Zaccc11/balance-car-stm32/src/Hardware/mpu6050.c

#include "mpu6050.h"
#include "sys.h"
#include "delay.h"
#include "usart.h"  
#include "MyI2C.h"
#include "MPU6050_Reg.h"
#define MPU6050_ADDRESS		0xD0		//MPU6050的I2C从机地址

//初始化MPU6050
//返回值:0,成功
//其他,错误代码
void MPU6050_Init(void)
{
	MyI2C_Init();									//先初始化底层的I2C
	
	/*MPU6050寄存器初始化，需要对照MPU6050手册的寄存器描述配置，此处仅配置了部分重要的寄存器*/
	MPU_Write_Byte(MPU_PWR_MGMT1_REG,0X80);	//复位MPU6050
	MPU_Write_Byte(MPU_PWR_MGMT1_REG,0X00);
	MPU6050_WriteReg(MPU6050_PWR_MGMT_1, 0x01);		//电源管理寄存器1，取消睡眠模式，选择时钟源为X轴陀螺仪
	MPU6050_WriteReg(MPU6050_PWR_MGMT_2, 0x00);		//电源管理寄存器2，保持默认值0，所有轴均不待机
	MPU6050_WriteReg(MPU6050_SMPLRT_DIV, 0x09);		//采样率分频寄存器，配置采样率
	MPU6050_WriteReg(MPU6050_CONFIG, 0x06);			//配置寄存器，配置DLPF
	MPU6050_WriteReg(MPU6050_GYRO_CONFIG, 0x18);	//陀螺仪配置寄存器，选择满量程为±2000°/s
	MPU6050_WriteReg(MPU6050_ACCEL_CONFIG, 0x18);	//加速度计配置寄存器，选择满量程为±16g
	MPU_Write_Byte(MPU_INTBP_CFG_REG,0X80);	//INT引脚低电平有效
}


uint8_t MPU_GetID(void){
	return MPU_Read_Byte(MPU_DEVICE_ID_REG);
}


void MPU6050_GetData(int16_t *AccX, int16_t *AccY, int16_t *AccZ, 
						int16_t *GyroX, int16_t *GyroY, int16_t *GyroZ)
{
	uint8_t DataH, DataL;								//定义数据高8位和低8位的变量
	
	DataH = MPU6050_ReadReg(MPU6050_ACCEL_XOUT_H);		//读取加速度计X轴的高8位数据
	DataL = MPU6050_ReadReg(MPU6050_ACCEL_XOUT_L);		//读取加速度计X轴的低8位数据
	*AccX = (DataH << 8) | DataL;						//数据拼接，通过输出参数返回
	
	DataH = MPU6050_ReadReg(MPU6050_ACCEL_YOUT_H);		//读取加速度计Y轴的高8位数据
	DataL = MPU6050_ReadReg(MPU6050_ACCEL_YOUT_L);		//读取加速度计Y轴的低8位数据
	*AccY = (DataH << 8) | DataL;						//数据拼接，通过输出参数返回
	
	DataH = MPU6050_ReadReg(MPU6050_ACCEL_ZOUT_H);		//读取加速度计Z轴的高8位数据
	DataL = MPU6050_ReadReg(MPU6050_ACCEL_ZOUT_L);		//读取加速度计Z轴的低8位数据
	*AccZ = (DataH << 8) | DataL;						//数据拼接，通过输出参数返回
	
	DataH = MPU6050_ReadReg(MPU6050_GYRO_XOUT_H);		//读取陀螺仪X轴的高8位数据
	DataL = MPU6050_ReadReg(MPU6050_GYRO_XOUT_L);		//读取陀螺仪X轴的低8位数据
	*GyroX = (DataH << 8) | DataL;						//数据拼接，通过输出参数返回
	
	DataH = MPU6050_ReadReg(MPU6050_GYRO_YOUT_H);		//读取陀螺仪Y轴的高8位数据
	DataL = MPU6050_ReadReg(MPU6050_GYRO_YOUT_L);		//读取陀螺仪Y轴的低8位数据
	*GyroY = (DataH << 8) | DataL;						//数据拼接，通过输出参数返回
	
	DataH = MPU6050_ReadReg(MPU6050_GYRO_ZOUT_H);		//读取陀螺仪Z轴的高8位数据
	DataL = MPU6050_ReadReg(MPU6050_GYRO_ZOUT_L);		//读取陀螺仪Z轴的低8位数据
	*GyroZ = (DataH << 8) | DataL;						//数据拼接，通过输出参数返回
}

uint8_t MPU6050_ReadReg(uint8_t RegAddress)
{
	uint8_t Data;
	
	MyI2C_Start();						//I2C起始
	MyI2C_SendByte(MPU6050_ADDRESS);	//发送从机地址，读写位为0，表示即将写入
	MyI2C_ReceiveAck();					//接收应答
	MyI2C_SendByte(RegAddress);			//发送寄存器地址
	MyI2C_ReceiveAck();					//接收应答
	
	MyI2C_Start();						//I2C重复起始
	MyI2C_SendByte(MPU6050_ADDRESS | 0x01);	//发送从机地址，读写位为1，表示即将读取
	MyI2C_ReceiveAck();					//接收应答
	Data = MyI2C_ReceiveByte();			//接收指定寄存器的数据
	MyI2C_SendAck(1);					//发送应答，给从机非应答，终止从机的数据输出
	MyI2C_Stop();						//I2C终止
	
	return Data;
}

u8 MPU_Get_Gyroscope(short *gx,short *gy,short *gz)
{
    u8 buf[6],res;  
	res=MPU_Read_Len(MPU_ADDR,MPU_GYRO_XOUTH_REG,6,buf);
	if(res==0)
	{
		*gx=((u16)buf[0]<<8)|buf[1];  
		*gy=((u16)buf[2]<<8)|buf[3];  
		*gz=((u16)buf[4]<<8)|buf[5];
	} 	
    return res;;
}

u8 MPU_Get_Accelerometer(short *ax,short *ay,short *az)
{
    u8 buf[6],res;  
	res=MPU_Read_Len(MPU_ADDR,MPU_ACCEL_XOUTH_REG,6,buf);
	if(res==0)
	{
		*ax=((u16)buf[0]<<8)|buf[1];  
		*ay=((u16)buf[2]<<8)|buf[3];  
		*az=((u16)buf[4]<<8)|buf[5];
	} 	
    return res;;
}


//IIC连续写
//addr:器件地址 
//reg:寄存器地址
//len:写入长度
//buf:数据区
//返回值:0,正常
//    其他,错误代码
u8 MPU_Write_Len(u8 addr,u8 reg,u8 len,u8 *buf)
{
	u8 i; 
    MPU_IIC_Start(); 
	MPU_IIC_Send_Byte((addr<<1)|0);//发送器件地址+写命令	
	if(MPU_IIC_Wait_Ack())	//等待应答
	{
		MPU_IIC_Stop();		 
		return 1;		
	}
    MPU_IIC_Send_Byte(reg);	//写寄存器地址
    MPU_IIC_Wait_Ack();		//等待应答
	for(i=0;i<len;i++)
	{
		MPU_IIC_Send_Byte(buf[i]);	//发送数据
		if(MPU_IIC_Wait_Ack())		//等待ACK
		{
			MPU_IIC_Stop();	 
			return 1;		 
		}		
	}    
    MPU_IIC_Stop();	 
	return 0;	
} 

//IIC连续读
//addr:器件地址
//reg:要读取的寄存器地址
//len:要读取的长度
//buf:读取到的数据存储区
//返回值:0,正常
//    其他,错误代码
u8 MPU_Read_Len(u8 addr,u8 reg,u8 len,u8 *buf)
{ 
 	MPU_IIC_Start(); 
	MPU_IIC_Send_Byte((addr<<1)|0);//发送器件地址+写命令	
	if(MPU_IIC_Wait_Ack())	//等待应答
	{
		MPU_IIC_Stop();		 
		return 1;		
	}
    MPU_IIC_Send_Byte(reg);	//写寄存器地址
    MPU_IIC_Wait_Ack();		//等待应答
    MPU_IIC_Start();
	MPU_IIC_Send_Byte((addr<<1)|1);//发送器件地址+读命令	
    MPU_IIC_Wait_Ack();		//等待应答 
	while(len)
	{
		if(len==1)*buf=MPU_IIC_Read_Byte(0);//读数据,发送nACK 
		else *buf=MPU_IIC_Read_Byte(1);		//读数据,发送ACK  
		len--;
		buf++; 
	}    
    MPU_IIC_Stop();	//产生一个停止条件 
	return 0;	
}

//IIC写一个字节 
//reg:寄存器地址
//data:数据
//返回值:0,正常
//    其他,错误代码
u8 MPU_Write_Byte(u8 reg,u8 data) 				 
{ 
    MPU_IIC_Start(); 
	MPU_IIC_Send_Byte((MPU_ADDR<<1)|0);//发送器件地址+写命令	
	if(MPU_IIC_Wait_Ack())	//等待应答
	{
		MPU_IIC_Stop();		 
		return 1;		
	}
    MPU_IIC_Send_Byte(reg);	//写寄存器地址
    MPU_IIC_Wait_Ack();		//等待应答 
	MPU_IIC_Send_Byte(data);//发送数据
	if(MPU_IIC_Wait_Ack())	//等待ACK
	{
		MPU_IIC_Stop();	 
		return 1;		 
	}		 
    MPU_IIC_Stop();	 
	return 0;
}

//IIC读一个字节 
//reg:寄存器地址 
//返回值:读到的数据
u8 MPU_Read_Byte(u8 reg)
{
	u8 res;
    MPU_IIC_Start(); 
	MPU_IIC_Send_Byte((MPU_ADDR<<1)|0);//发送器件地址+写命令	
	MPU_IIC_Wait_Ack();		//等待应答 
    MPU_IIC_Send_Byte(reg);	//写寄存器地址
    MPU_IIC_Wait_Ack();		//等待应答
    MPU_IIC_Start();
	MPU_IIC_Send_Byte((MPU_ADDR<<1)|1);//发送器件地址+读命令	
    MPU_IIC_Wait_Ack();		//等待应答 
	res=MPU_IIC_Read_Byte(0);//读取数据,发送nACK 
    MPU_IIC_Stop();			//产生一个停止条件 
	return res;		
}



void MPU6050_WriteReg(uint8_t RegAddress, uint8_t Data)
{
	MyI2C_Start();						//I2C起始
	MyI2C_SendByte(MPU6050_ADDRESS);	//发送从机地址，读写位为0，表示即将写入
	MyI2C_ReceiveAck();					//接收应答
	MyI2C_SendByte(RegAddress);			//发送寄存器地址
	MyI2C_ReceiveAck();					//接收应答
	MyI2C_SendByte(Data);				//发送要写入寄存器的数据
	MyI2C_ReceiveAck();					//接收应答
	MyI2C_Stop();						//I2C终止
}
