Zaccc11/balance-car-stm32/src/Hardware/EXTI.c

#include "stm32f10x.h"

void MPU6050_EXTI_Init(void) {
	 EXTI_InitTypeDef EXTI_InitStructure;
	 GPIO_InitTypeDef GPIO_InitStructure;
	 RCC_APB2PeriphClockCmd(RCC_APB2Periph_GPIOB | RCC_APB2Periph_AFIO, ENABLE);
	 GPIO_InitStructure.GPIO_Mode = GPIO_Mode_IPU;
	 GPIO_InitStructure.GPIO_Pin = GPIO_Pin_5;
	 GPIO_InitStructure.GPIO_Speed = GPIO_Speed_50MHz;
	 GPIO_Init(GPIOB, &GPIO_InitStructure);
	 
	 GPIO_EXTILineConfig(GPIO_PortSourceGPIOB,GPIO_PinSource5);
	 
	 EXTI_InitStructure.EXTI_Line = EXTI_Line5;
	 EXTI_InitStructure.EXTI_LineCmd = ENABLE;
	 EXTI_InitStructure.EXTI_Mode =EXTI_Mode_Interrupt;
	 EXTI_InitStructure.EXTI_Trigger = EXTI_Trigger_Falling;
	 EXTI_Init(&EXTI_InitStructure);
}

	
