Zaccc11/balance-car-stm32/src/Hardware/MyI2C.c

#include "stm32f10x.h"                  // Device header
#include "Delay.h"
//SCL = PB4 ,SDA = PB3;
void MyI2C_W_SCL(uint8_t BitValue)
{
	GPIO_WriteBit(GPIOB, GPIO_Pin_4, (BitAction)BitValue);
	delay_us(10);
}

void MyI2C_W_SDA(uint8_t BitValue)
{
	GPIO_WriteBit(GPIOB, GPIO_Pin_3, (BitAction)BitValue);
	delay_us(10);
}

uint8_t MyI2C_R_SDA(void)
{
	uint8_t BitValue;
	BitValue = GPIO_ReadInputDataBit(GPIOB, GPIO_Pin_3);
	delay_us(10);
	return BitValue;
}

void MyI2C_Init(void)
{
	RCC_APB2PeriphClockCmd(RCC_APB2Periph_GPIOB, ENABLE);
	RCC_APB2PeriphClockCmd(RCC_APB2Periph_AFIO, ENABLE);
	GPIO_PinRemapConfig(GPIO_Remap_SWJ_JTAGDisable, ENABLE);
	
	//SCL
	GPIO_InitTypeDef GPIO_InitStructure;
	GPIO_InitStructure.GPIO_Mode = GPIO_Mode_Out_PP;
	GPIO_InitStructure.GPIO_Pin = GPIO_Pin_4;
	GPIO_InitStructure.GPIO_Speed = GPIO_Speed_50MHz;
	GPIO_Init(GPIOB, &GPIO_InitStructure);
	//SDA
	GPIO_InitStructure.GPIO_Mode = GPIO_Mode_Out_OD;
	GPIO_InitStructure.GPIO_Pin = GPIO_Pin_3;
	GPIO_InitStructure.GPIO_Speed = GPIO_Speed_50MHz;
	GPIO_Init(GPIOB, &GPIO_InitStructure);
	
	GPIO_SetBits(GPIOB, GPIO_Pin_3 | GPIO_Pin_4);
}

void MyI2C_Start(void)
{
	MyI2C_W_SDA(1);
	MyI2C_W_SCL(1);
	MyI2C_W_SDA(0);
	MyI2C_W_SCL(0);
}

void MyI2C_Stop(void)
{
	MyI2C_W_SDA(0);
	MyI2C_W_SCL(1);
	MyI2C_W_SDA(1);
}

void MyI2C_SendByte(uint8_t Byte)
{
	uint8_t i;
	for (i = 0; i < 8; i ++)
	{
		MyI2C_W_SDA(!!(Byte & (0x80 >> i)));
		MyI2C_W_SCL(1);
		MyI2C_W_SCL(0);
	}
}

uint8_t MyI2C_ReceiveByte(void)
{
	uint8_t i, Byte = 0x00;
	MyI2C_W_SDA(1);
	for (i = 0; i < 8; i ++)
	{
		MyI2C_W_SCL(1);
		if (MyI2C_R_SDA()){Byte |= (0x80 >> i);}
		MyI2C_W_SCL(0);
	}
	return Byte;
}

void MyI2C_SendAck(uint8_t AckBit)
{
	MyI2C_W_SDA(AckBit);
	MyI2C_W_SCL(1);
	MyI2C_W_SCL(0);
}

uint8_t MyI2C_ReceiveAck(void)
{
	uint8_t AckBit;
	MyI2C_W_SDA(1);
	MyI2C_W_SCL(1);
	AckBit = MyI2C_R_SDA();
	MyI2C_W_SCL(0);
	return AckBit;
}
