Zaccc11/balance-car-stm32/src/Hardware/usart.c

#include "stm32f10x.h"
#include "usart.h"	  
#include "stdio.h"
#if SYSTEM_SUPPORT_OS
#include "includes.h"					//ucos 使用	  
#endif
//////////////////////////////////////////////////////////////////
//加入以下代码,支持printf函数,而不需要选择use MicroLIB	  
#if 1
#pragma import(__use_no_semihosting)             
//标准库需要的支持函数                 
struct __FILE 
{ 
	int handle; 
}; 

FILE __stdout;       
//定义_sys_exit()以避免使用半主机模式    
void _sys_exit(int x) 
{ 
	x = x; 
} 
//重定义fputc函数 
u8 Flag_Stop=1,Flag_Show=0;
int fputc(int ch, FILE *f)
{      
	if(Flag_Show==0)
	{	
	  while((USART3->SR&0X40)==0);//Flag_Show=0  使用串口3   
	  USART3->DR = (u8) ch;      
	}
	else
	{	
		while((USART1->SR&0X40)==0);//Flag_Show!=0  使用串口1   
		USART1->DR = (u8) ch;      
	}	
	return ch;
}
#endif 



void uart1_init(u32 bound)
{
  //GPIO端口设置
  GPIO_InitTypeDef GPIO_InitStructure;
	USART_InitTypeDef USART_InitStructure;
	 
	RCC_APB2PeriphClockCmd(RCC_APB2Periph_USART1|RCC_APB2Periph_GPIOB, ENABLE);	//使能USART1，GPIOB时钟
  
	//USART1_TX   GPIOB.11
  GPIO_InitStructure.GPIO_Pin = GPIO_Pin_11; //PB11
  GPIO_InitStructure.GPIO_Speed = GPIO_Speed_50MHz;
  GPIO_InitStructure.GPIO_Mode = GPIO_Mode_AF_PP;	//复用推挽输出
  GPIO_Init(GPIOB, &GPIO_InitStructure);//初始化GPIOB.11
   
  //USART1_RX	  GPIOA.10初始化
  GPIO_InitStructure.GPIO_Pin = GPIO_Pin_10;//PB11
  GPIO_InitStructure.GPIO_Mode = GPIO_Mode_IN_FLOATING;//浮空输入
  GPIO_Init(GPIOB, &GPIO_InitStructure);//初始化GPIOA.10  
   //USART 初始化设置

	USART_InitStructure.USART_BaudRate = bound;//串口波特率
	USART_InitStructure.USART_WordLength = USART_WordLength_8b;//字长为8位数据格式
	USART_InitStructure.USART_StopBits = USART_StopBits_1;//一个停止位
	USART_InitStructure.USART_Parity = USART_Parity_No;//无奇偶校验位
	USART_InitStructure.USART_HardwareFlowControl = USART_HardwareFlowControl_None;//无硬件数据流控制
	USART_InitStructure.USART_Mode = USART_Mode_Rx | USART_Mode_Tx;	//收发模式

  USART_Init(USART1, &USART_InitStructure); //初始化串口1
  USART_ITConfig(USART1, USART_IT_RXNE, DISABLE);//开启串口接受中断
  USART_Cmd(USART1, ENABLE);                    //使能串口1 

}

u8 USART_RX_BUF[64];     //接收缓冲,最大64个字节.
//接收状态
//bit7，接收完成标志
//bit6，接收到0x0d
//bit5~0，接收到的有效字节数目
u8 USART_RX_STA=0;       //接收状态标记

void USART1_IRQHandler(void)                	//串口1中断服务程序
	{
	u8 Res;
	if(USART_GetITStatus(USART1, USART_IT_RXNE) != RESET)  //接收中断(接收到的数据必须是0x0d 0x0a结尾)
		{
		Res =USART_ReceiveData(USART1);//(USART1->DR);	//读取接收到的数据
		
		if((USART_RX_STA&0x80)==0)//接收未完成
			{
			if(USART_RX_STA&0x40)//接收到了0x0d
				{
				if(Res!=0x0a)USART_RX_STA=0;//接收错误,重新开始
				else USART_RX_STA|=0x80;	//接收完成了 
				}
			else //还没收到0X0D
				{	
				if(Res==0x0d)USART_RX_STA|=0x40;
				else
					{
					USART_RX_BUF[USART_RX_STA&0X3F]=Res ;
					USART_RX_STA++;
					if(USART_RX_STA>63)USART_RX_STA=0;//接收数据错误,重新开始接收	  
					}		 
				}
			}   		 
     } 
} 
